hotkeysoft/repeatElectronicGame-kicad/src/RepeatGame/rom.h

const uint8_t rom[] PROGMEM = {
	0x3C, 0x46, 0x37, 0x87, 0x3C, 0x46, 0x33, 0x24, 0x0D, 0x40, 0x6F, 0x07, 0x90, 0x61, 0x68, 0x9C, 
	0x07, 0x95, 0x6E, 0x62, 0x9C, 0x07, 0x9A, 0x66, 0x6E, 0x9C, 0x62, 0x6F, 0x03, 0x4E, 0x21, 0x2D, 
	0x03, 0x0A, 0x44, 0x22, 0xA5, 0x2C, 0xA4, 0x2C, 0xA7, 0x46, 0x3B, 0xAF, 0x09, 0xBB, 0xB5, 0x40, 
	0x2A, 0xBC, 0x6F, 0x2A, 0x9C, 0x4E, 0x0C, 0x2C, 0xB6, 0x3E, 0x0F, 0x21, 0xBD, 0xB4, 0x00, 0x00, 
	0x0D, 0x3C, 0x40, 0x67, 0x67, 0x03, 0x4E, 0x21, 0x2D, 0x03, 0x0A, 0x4A, 0x07, 0x8C, 0x07, 0x8E, 
	0x2C, 0x8C, 0x40, 0x2A, 0x85, 0x6F, 0x2A, 0x85, 0x0F, 0x4C, 0x21, 0x48, 0x22, 0x02, 0xA7, 0x44, 
	0x21, 0x40, 0x22, 0x02, 0xAA, 0x46, 0x0F, 0x40, 0x26, 0xAD, 0x40, 0x68, 0x0F, 0x60, 0x28, 0x03, 
	0x0F, 0x48, 0x25, 0xBE, 0x40, 0x25, 0x4A, 0x20, 0x3E, 0x03, 0x4A, 0x21, 0x46, 0x0F, 0x0E, 0xB4, 
	0x3C, 0x40, 0x6F, 0x6F, 0x6F, 0x66, 0x60, 0x8F, 0x3C, 0x40, 0x6F, 0x6F, 0x6F, 0x63, 0x60, 0x03, 
	0x09, 0x9A, 0x40, 0x2A, 0x8F, 0x6F, 0x5A, 0x93, 0x3E, 0x0F, 0x4F, 0x07, 0x9B, 0x2C, 0x9B, 0x09, 
	0xA2, 0x90, 0x08, 0x70, 0x90, 0x40, 0x78, 0xAF, 0x2B, 0x7C, 0xAF, 0x2B, 0x7E, 0xAF, 0x2B, 0x23, 
	0x3E, 0x4E, 0x03, 0x0F, 0x03, 0x4A, 0x21, 0x10, 0xC4, 0x16, 0xD0, 0x40, 0x2A, 0xB4, 0x1E, 0x95, 
	0x48, 0x21, 0x3F, 0x01, 0x87, 0x3D, 0x01, 0x24, 0x21, 0x3E, 0x40, 0x2E, 0x70, 0x96, 0x30, 0x32, 
	0x39, 0x93, 0x34, 0x3B, 0x96, 0x36, 0x35, 0x37, 0x2E, 0x0F, 0x60, 0x2F, 0x0E, 0x3C, 0x42, 0x25, 
	0xFE, 0x18, 0xF1, 0x1A, 0xEF, 0x03, 0x3E, 0x4A, 0x28, 0xB5, 0x03, 0x3C, 0x48, 0x21, 0x2C, 0x03, 
	0x2B, 0x2B, 0x56, 0xAD, 0x9B, 0x42, 0x09, 0xB5, 0x1A, 0x37, 0x26, 0x84, 0x12, 0x80, 0x0E, 0x0F, 
	0x40, 0x60, 0x60, 0x1C, 0xC0, 0x10, 0xC4, 0x16, 0xD7, 0x18, 0xD9, 0x56, 0x83, 0x42, 0x1E, 0x3B, 
	0x95, 0x16, 0x38, 0x80, 0x40, 0x60, 0x60, 0x14, 0xC0, 0x5E, 0xB5, 0x1C, 0xC0, 0x4E, 0x22, 0x02, 
	0xB8, 0x10, 0xC0, 0x18, 0xD9, 0x56, 0x97, 0x44, 0x26, 0xAE, 0x68, 0x16, 0xD3, 0x80, 0x1E, 0x60, 
	0x28, 0xBA, 0x12, 0x03, 0xAB, 0x1C, 0xC0, 0x24, 0x18, 0xC0, 0x10, 0xF5, 0x16, 0xB0, 0x00, 0x00, 
	0x44, 0x26, 0x85, 0x12, 0x80, 0x14, 0xC0, 0x12, 0x5E, 0xB5, 0x1A, 0x4C, 0x21, 0x48, 0x22, 0x02, 
	0x94, 0x40, 0x26, 0xA5, 0x1C, 0xC0, 0x4E, 0x22, 0x12, 0x02, 0xB8, 0x10, 0xC0, 0x18, 0xD9, 0x56, 
	0x80, 0x16, 0xD3, 0x16, 0x80, 0x4E, 0x21, 0x25, 0x25, 0x25, 0x46, 0x03, 0x48, 0x21, 0x46, 0x01, 
	0xB6, 0x01, 0x2E, 0x22, 0x3D, 0xB9, 0x2E, 0x22, 0x3F, 0x0F, 0x35, 0x37, 0x25, 0x03, 0x3E, 0x94, 
	0x44, 0x26, 0x89, 0x68, 0x40, 0x60, 0x60, 0x1A, 0x80, 0x60, 0x1E, 0x28, 0xBA, 0x03, 0x16, 0x84, 
	0x46, 0x60, 0xA0, 0x46, 0x6F, 0x6A, 0xA1, 0x4C, 0x21, 0x2D, 0x07, 0x46, 0x03, 0x34, 0x32, 0x4E, 
	0x60, 0x03, 0x41, 0x07, 0xA3, 0x07, 0xA5, 0x2C, 0xA3, 0x46, 0x2A, 0xA1, 0x6F, 0x2A, 0xA1, 0x0F, 
	0x4C, 0x21, 0x4A, 0x7C, 0xB9, 0x75, 0xB8, 0x64, 0x68, 0x60, 0x16, 0xD3, 0x40, 0x6E, 0x14, 0xB4, 
	0x3C, 0x46, 0x30, 0x4E, 0x66, 0x10, 0xF5, 0x16, 0xD3, 0x4A, 0x60, 0x2F, 0x10, 0xC4, 0x16, 0xD0, 
	0x4A, 0x28, 0x03, 0x7C, 0x8C, 0x14, 0xC8, 0x5E, 0x89, 0x3C, 0x46, 0x74, 0xAB, 0x38, 0xA6, 0x3E, 
	0x44, 0x60, 0x60, 0x0F, 0x1C, 0xB5, 0x18, 0xC1, 0x10, 0xF5, 0x95, 0x78, 0xB4, 0x38, 0xA6, 0x3E, 
	0x42, 0x33, 0x12, 0x80, 0x34, 0xDF, 0x03, 0x4A, 0x1C, 0x9A, 0x44, 0x68, 0x4A, 0x6C, 0x16, 0xBA, 
	};
